mistay/s0http/media/IMG_1309.JPG

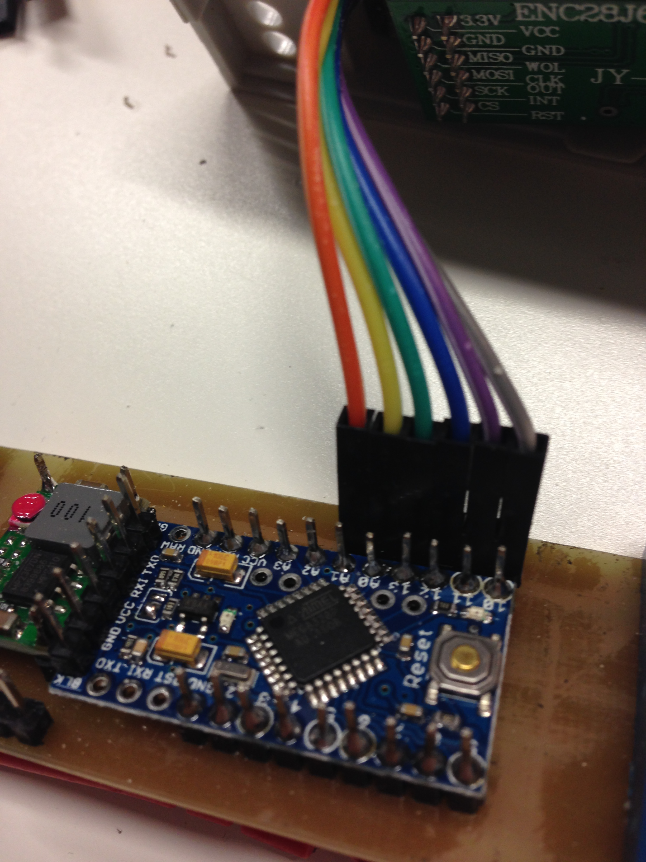
media/IMG_1309.JPG
