mistay/s0http/media/IMG_1310.JPG

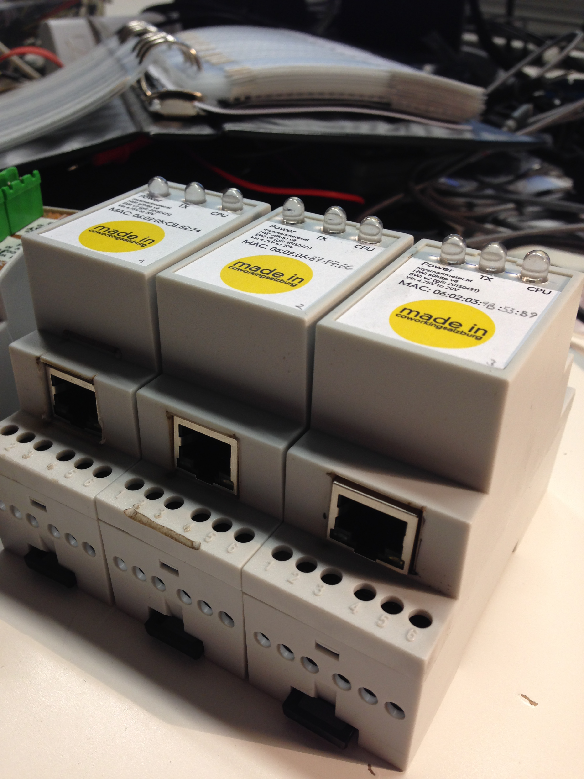
media/IMG_1310.JPG
