mistay/s0http/media/IMG_1311.JPG

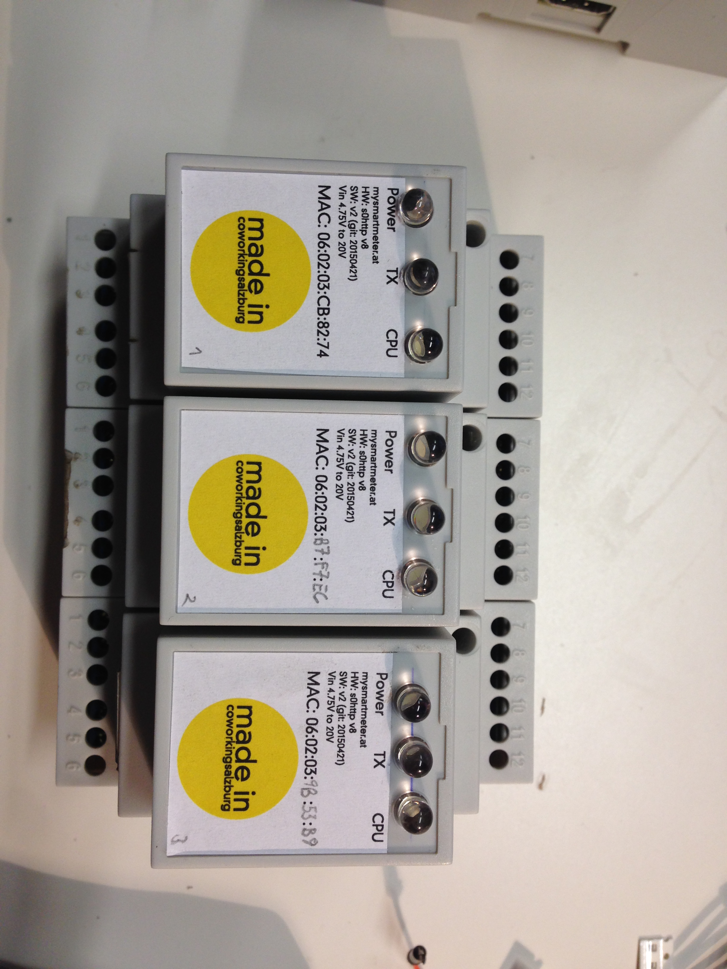
media/IMG_1311.JPG
