mistay/s0http/media/IMG_1312.JPG

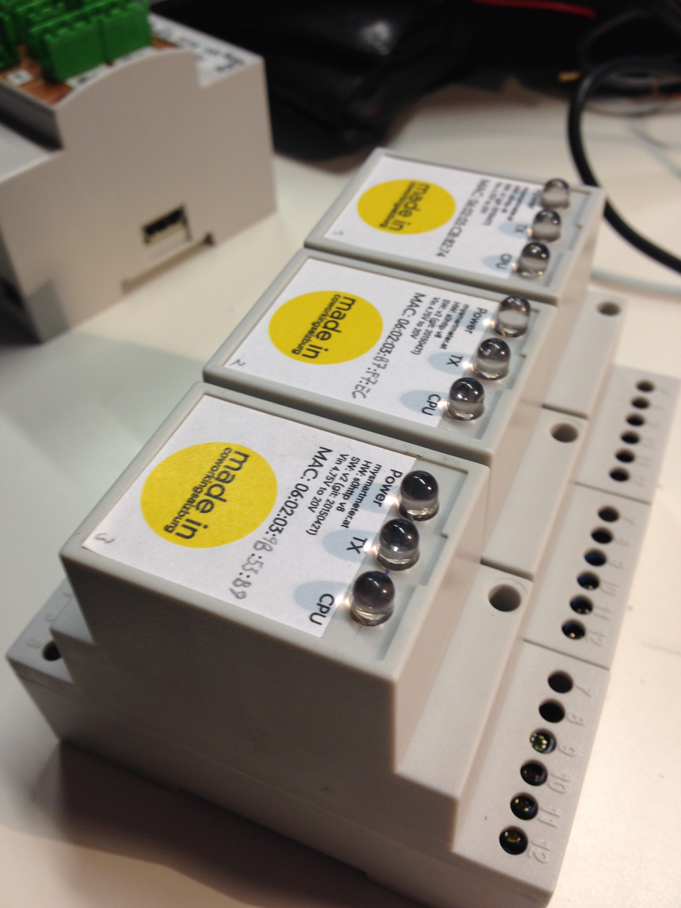
media/IMG_1312.JPG
