mistay/s0http/media/IMG_1313.JPG

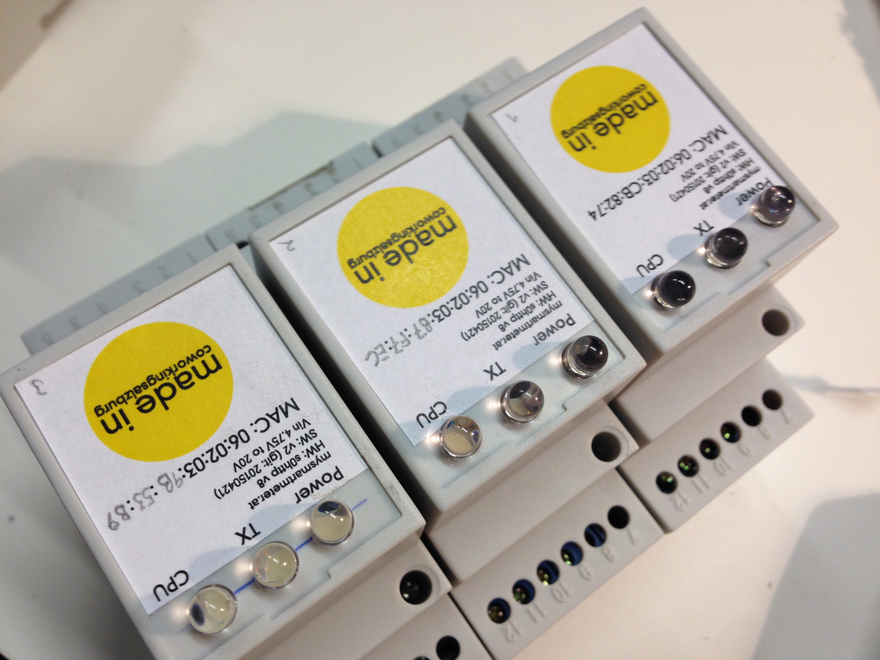
media/IMG_1313.JPG
