mistay/s0http/media/IMG_1314.JPG

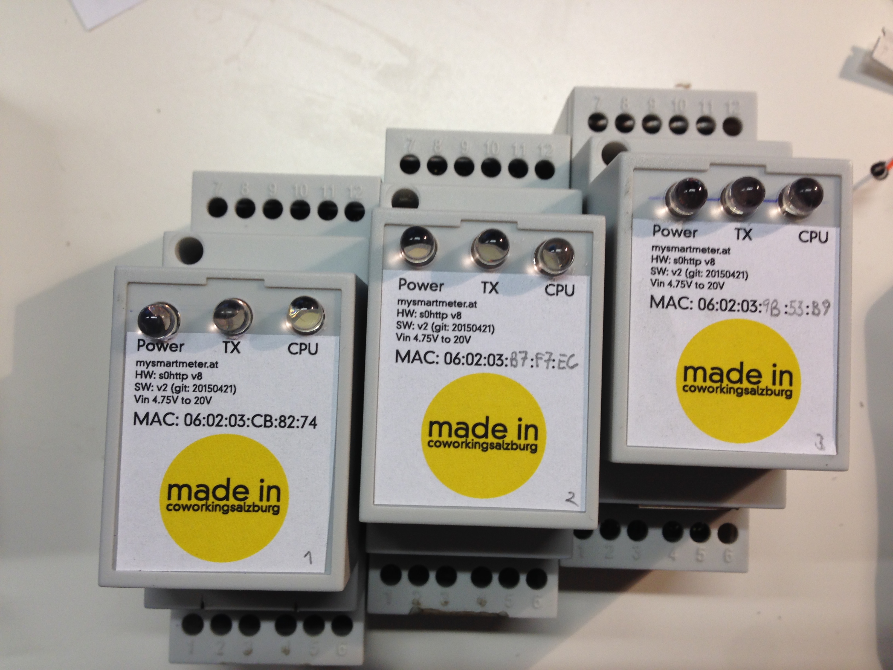
media/IMG_1314.JPG
