mistay/s0http/media/IMG_6536.JPG

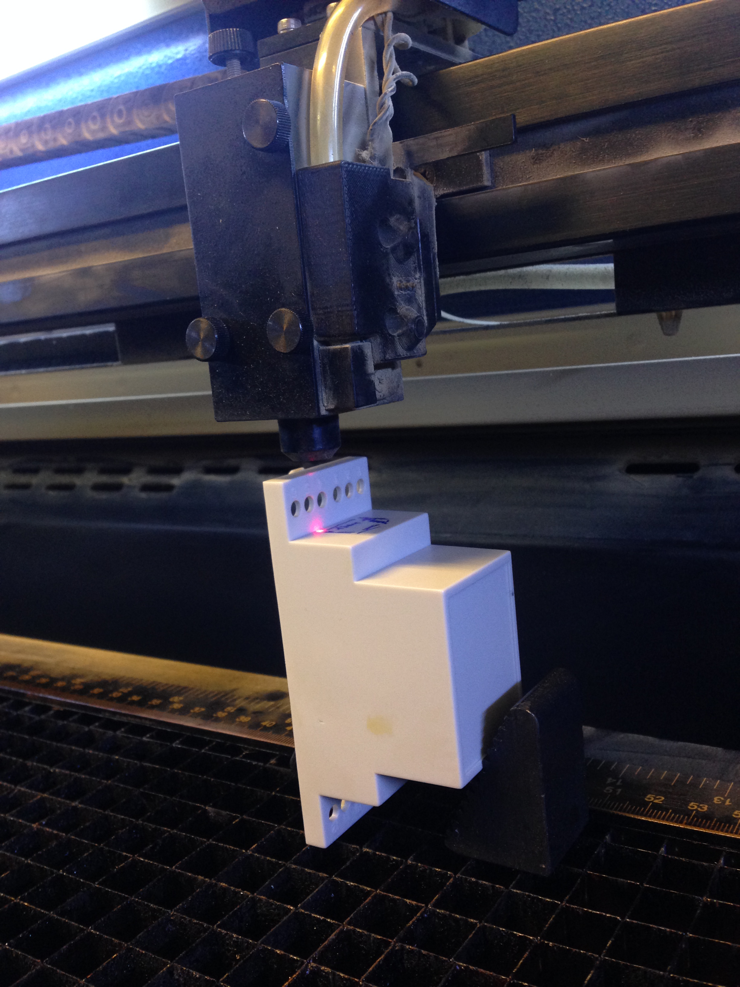
media/IMG_6536.JPG
