mistay/s0http/media/IMG_6537.JPG

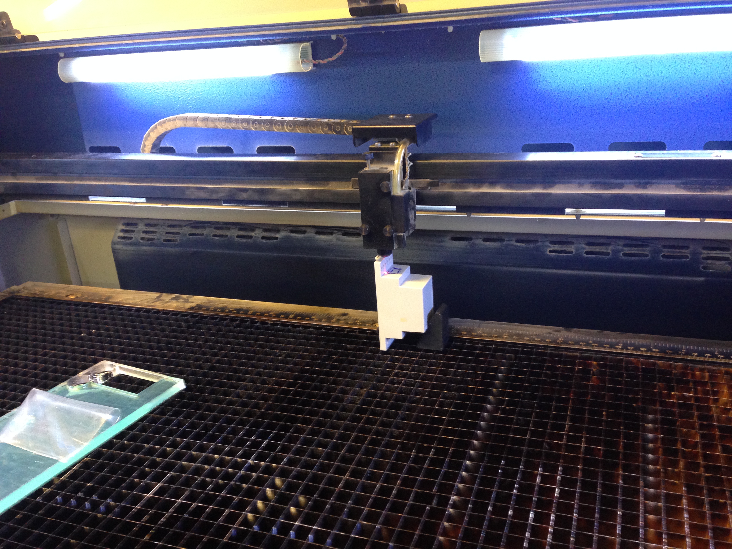
media/IMG_6537.JPG
