mistay/s0http/media/IMG_6538.JPG

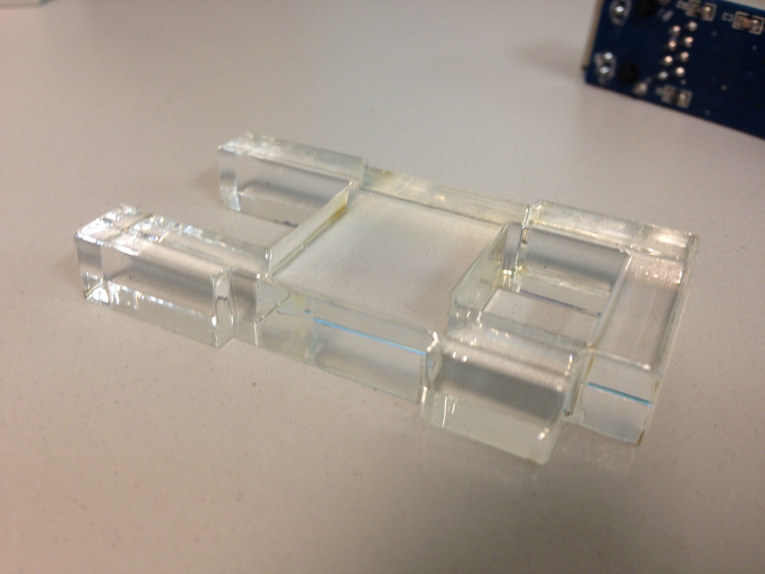
media/IMG_6538.JPG
