mistay/s0http/media/IMG_6539.JPG

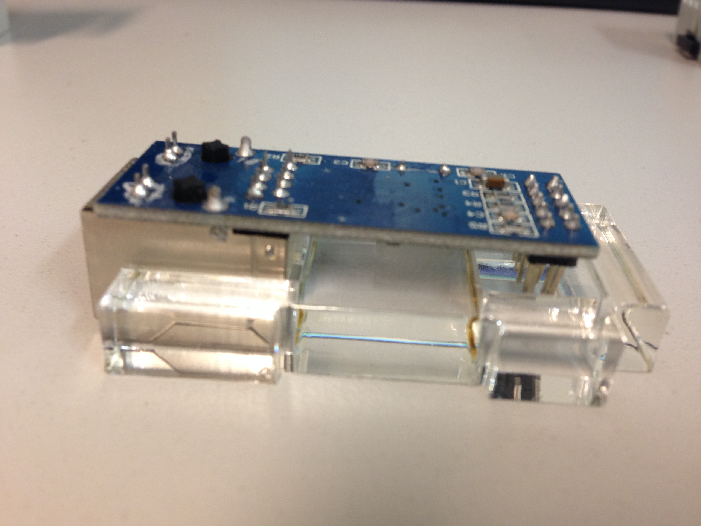
media/IMG_6539.JPG
