mistay/s0http/media/IMG_6540.JPG

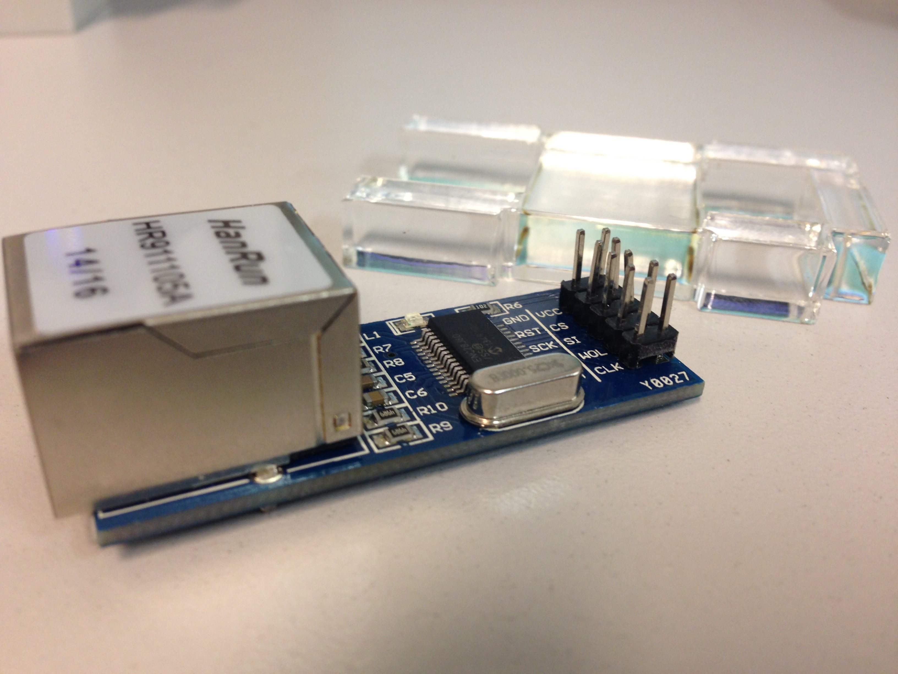
media/IMG_6540.JPG
