mistay/s0http/media/IMG_6542.JPG

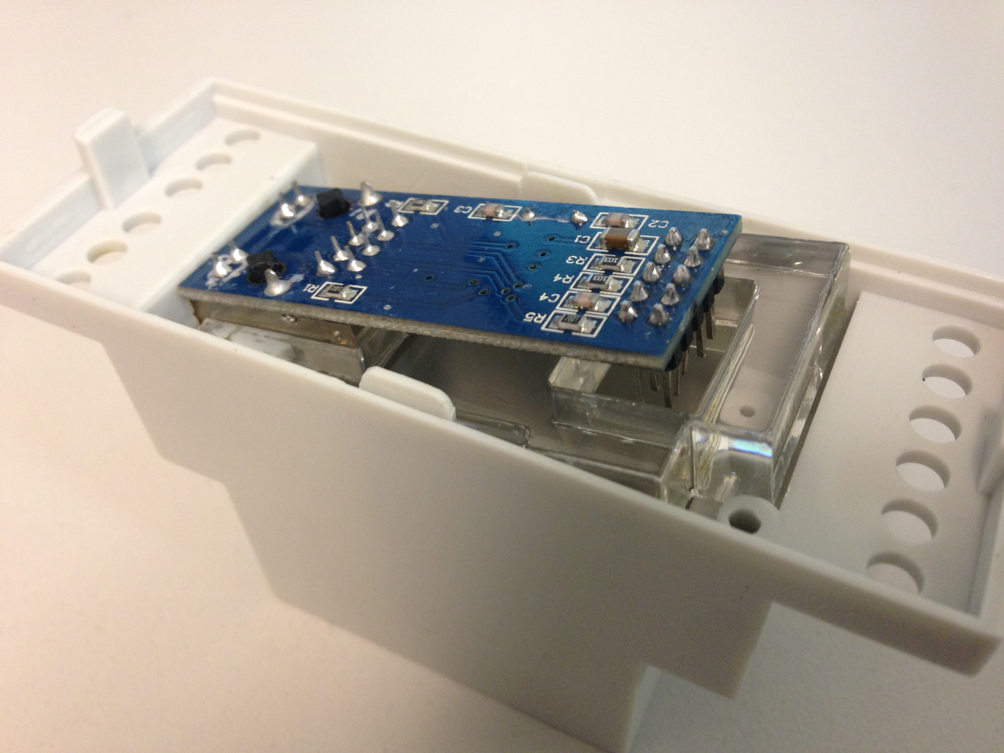
media/IMG_6542.JPG
