mistay/s0http/media/IMG_6543.JPG

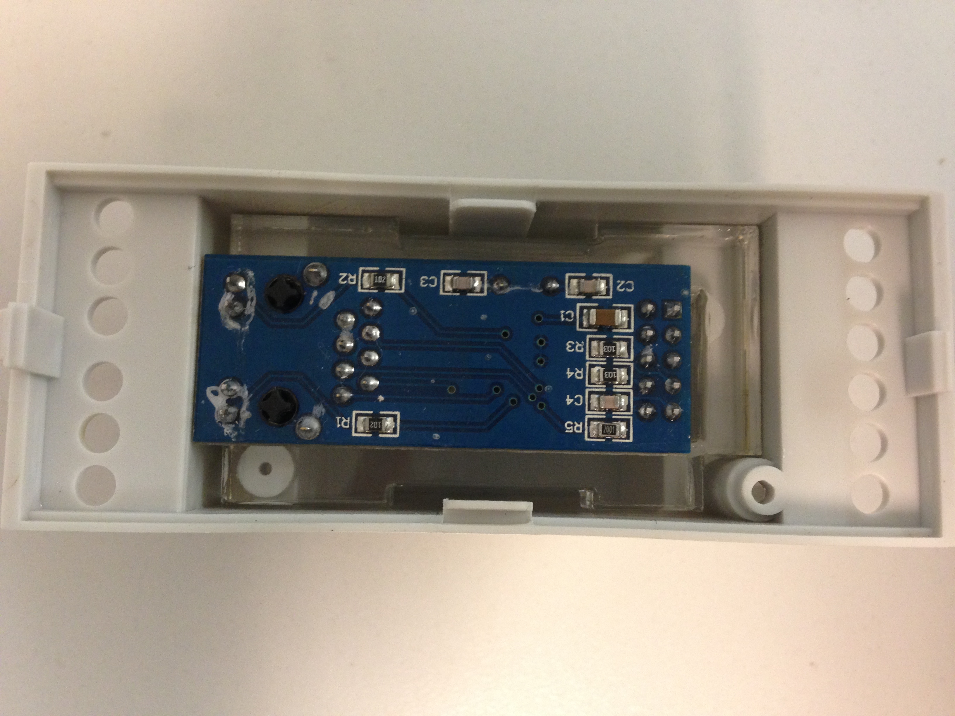
media/IMG_6543.JPG
