mistay/s0http/media/IMG_6544.JPG

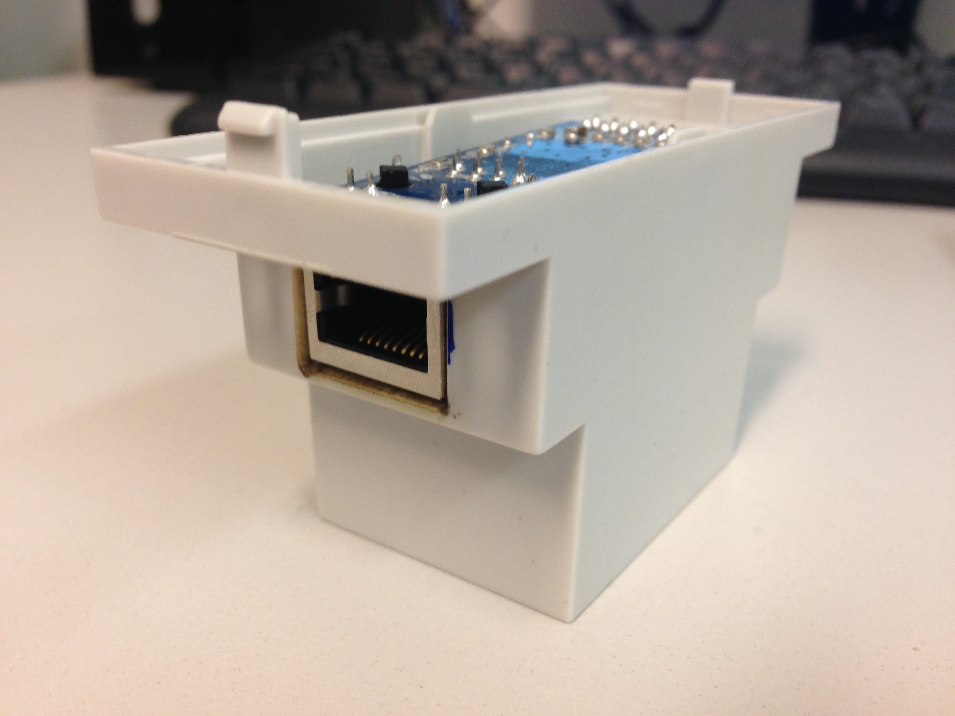
media/IMG_6544.JPG
