mistay/s0http/media/IMG_7528.JPG

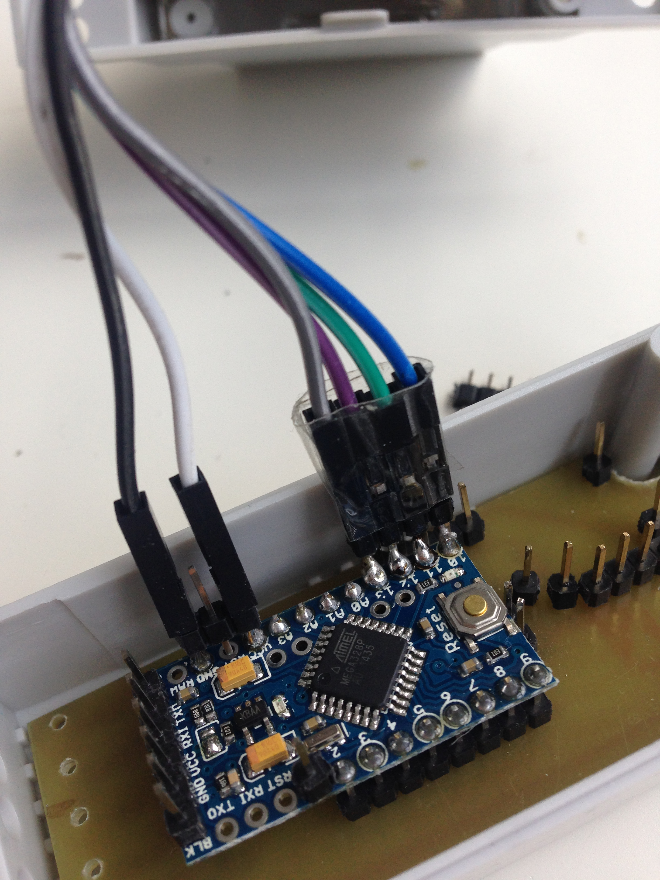
media/IMG_7528.JPG
