mistay/s0http/media/IMG_7529.JPG

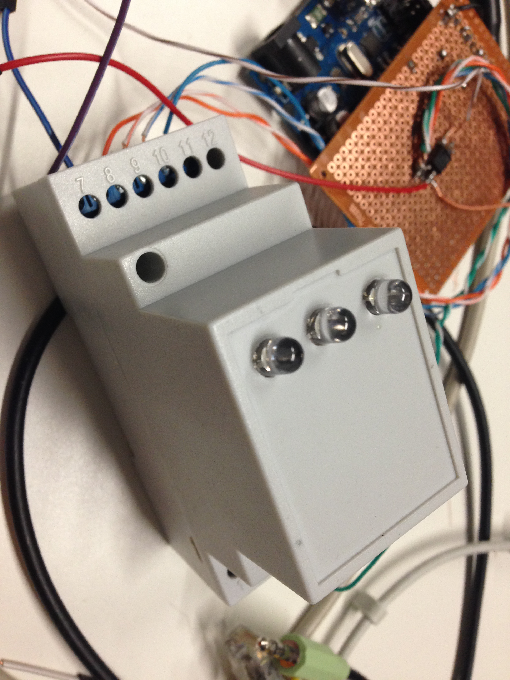
media/IMG_7529.JPG
