mistay/s0http/media/IMG_7530.JPG

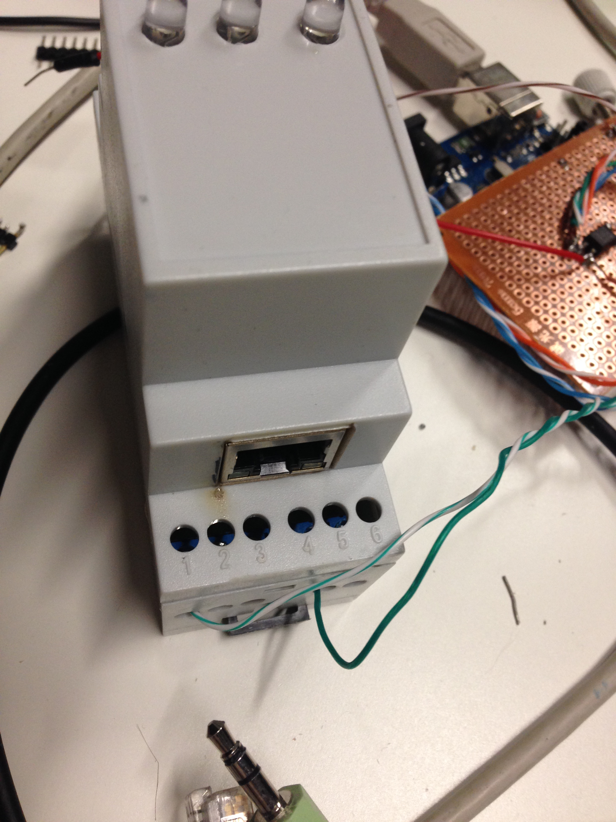
media/IMG_7530.JPG
