mistay/s0http/media/IMG_7531.JPG

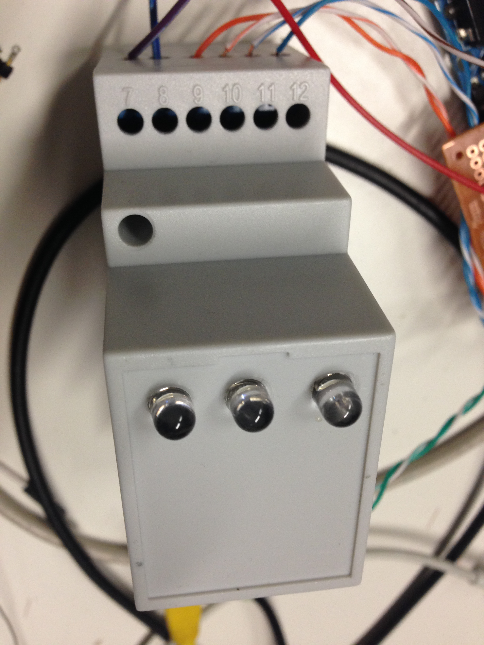
media/IMG_7531.JPG
