mistay/s0http/media/IMG_7536.JPG

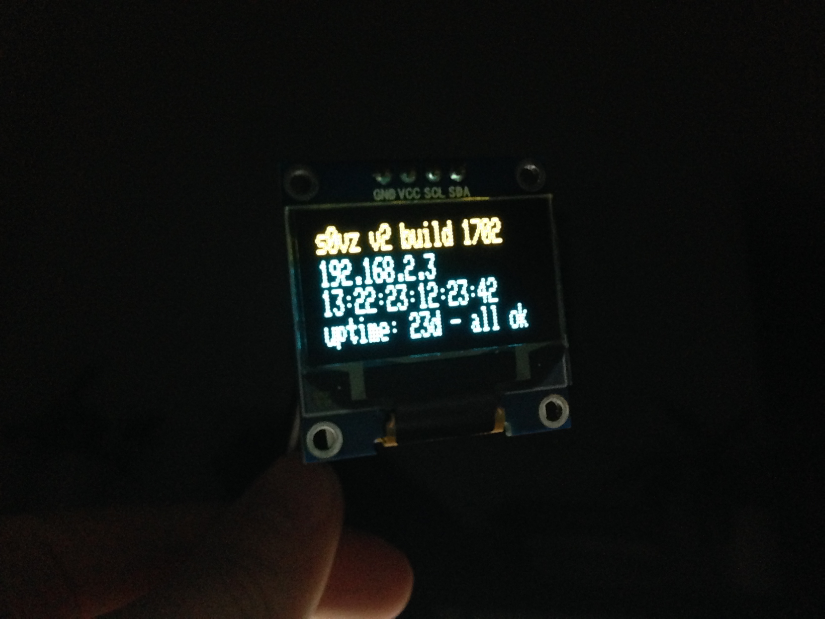
media/IMG_7536.JPG
