mistay/s0http/media/IMG_7617.JPG

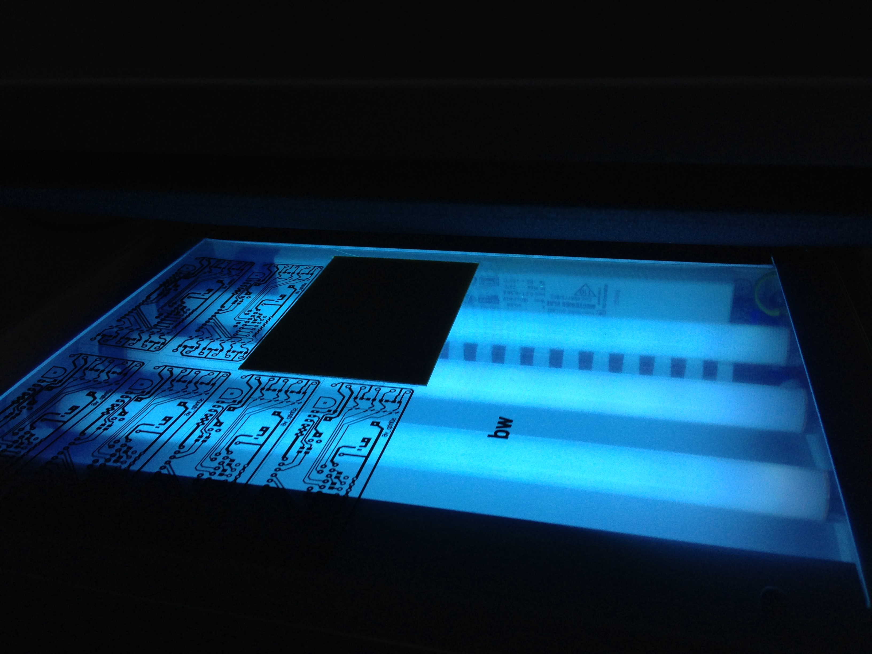
media/IMG_7617.JPG
