mistay/s0http/media/IMG_7618.JPG

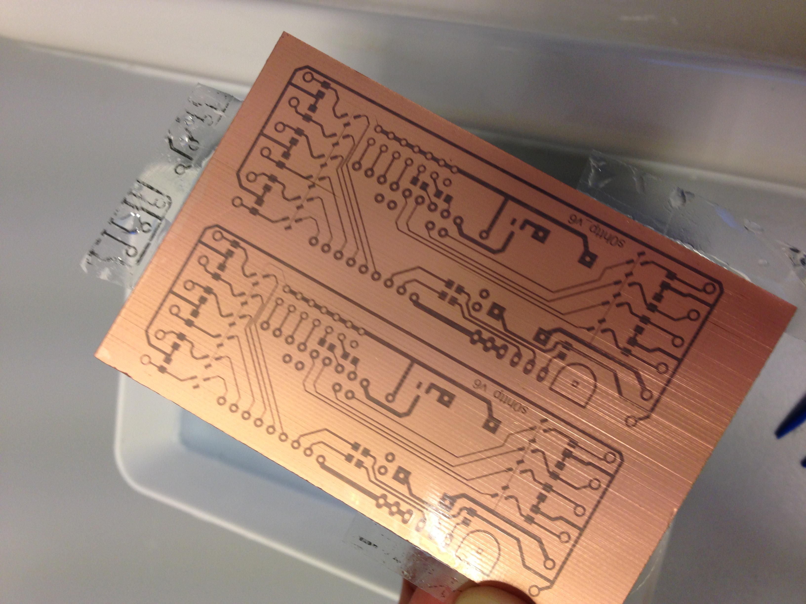
media/IMG_7618.JPG
