mistay/s0http/media/IMG_7619.JPG

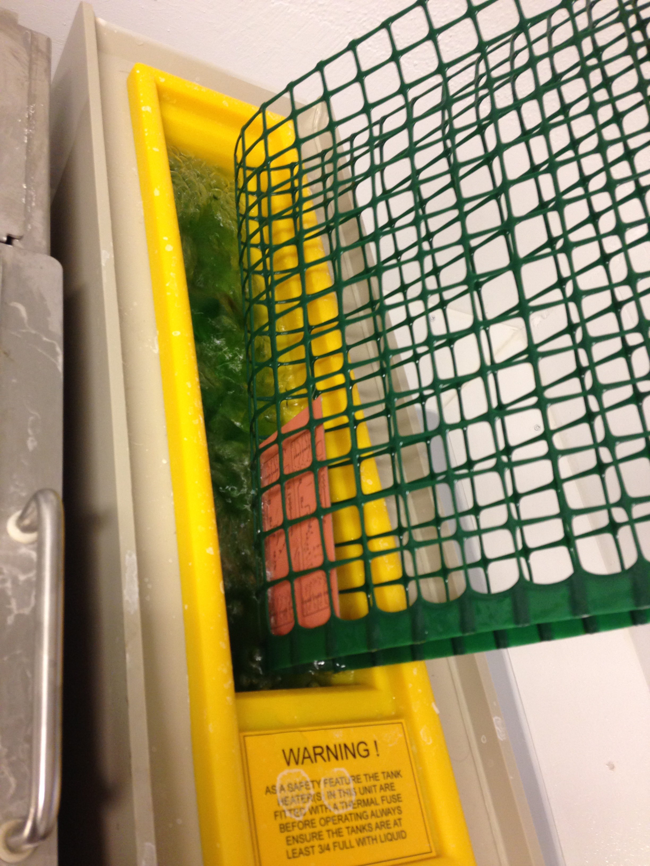
media/IMG_7619.JPG
