mistay/s0http/media/IMG_7620.JPG

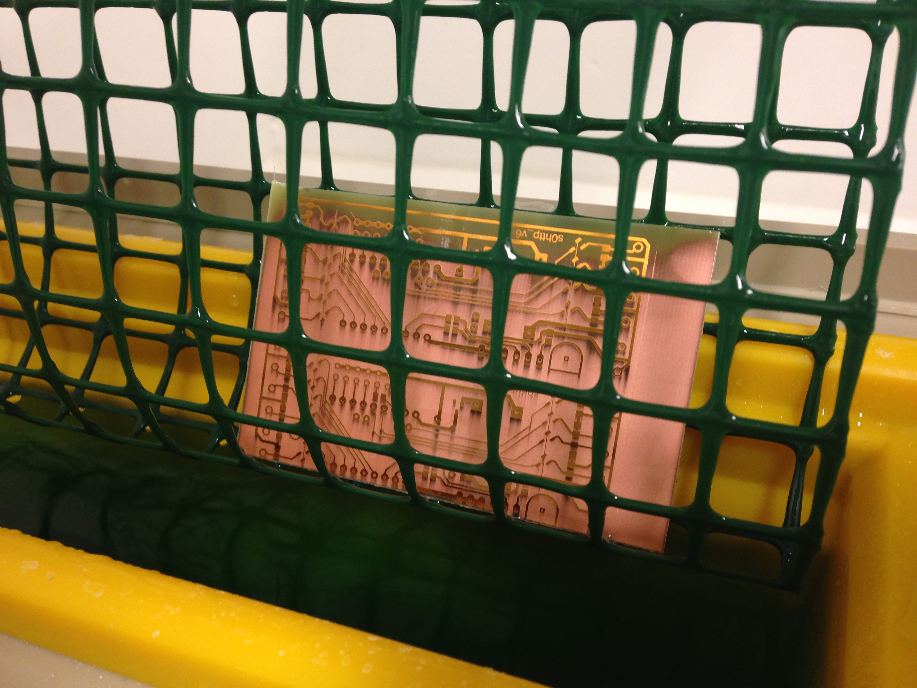
media/IMG_7620.JPG
