mistay/s0http/media/IMG_7635.JPG

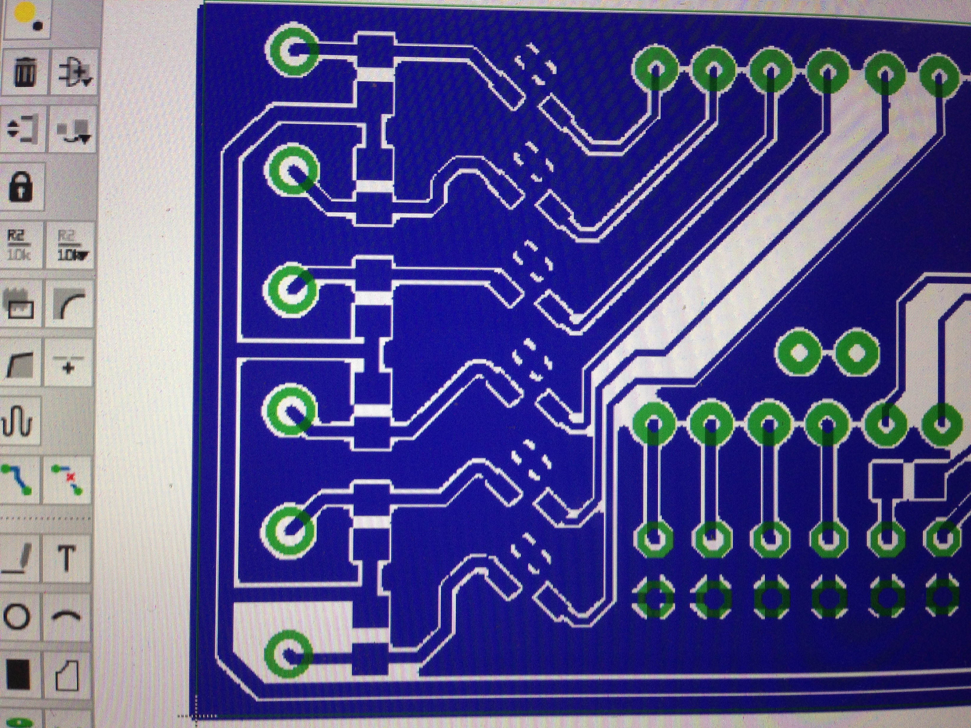
media/IMG_7635.JPG
