mistay/s0http/media/IMG_7978.JPG

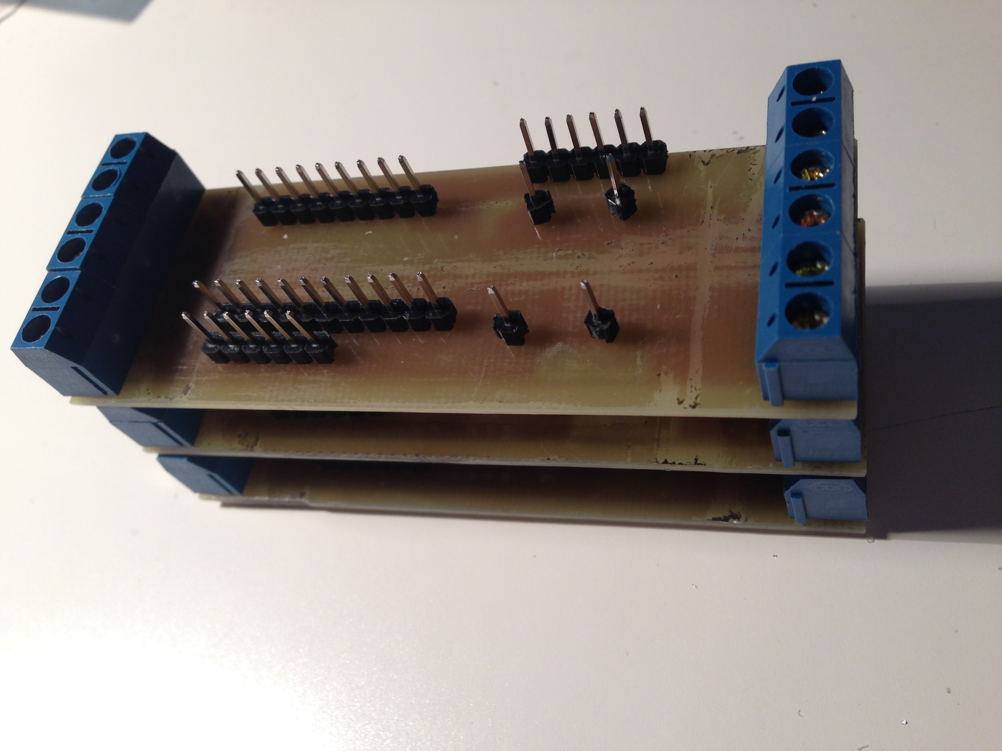
media/IMG_7978.JPG
