mistay/s0http/media/IMG_7979.JPG

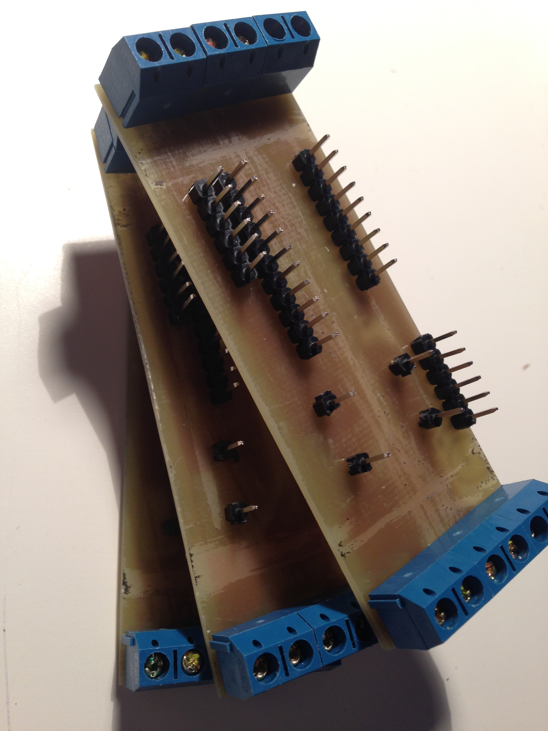
media/IMG_7979.JPG
