mistay/s0http/media/IMG_7980.JPG

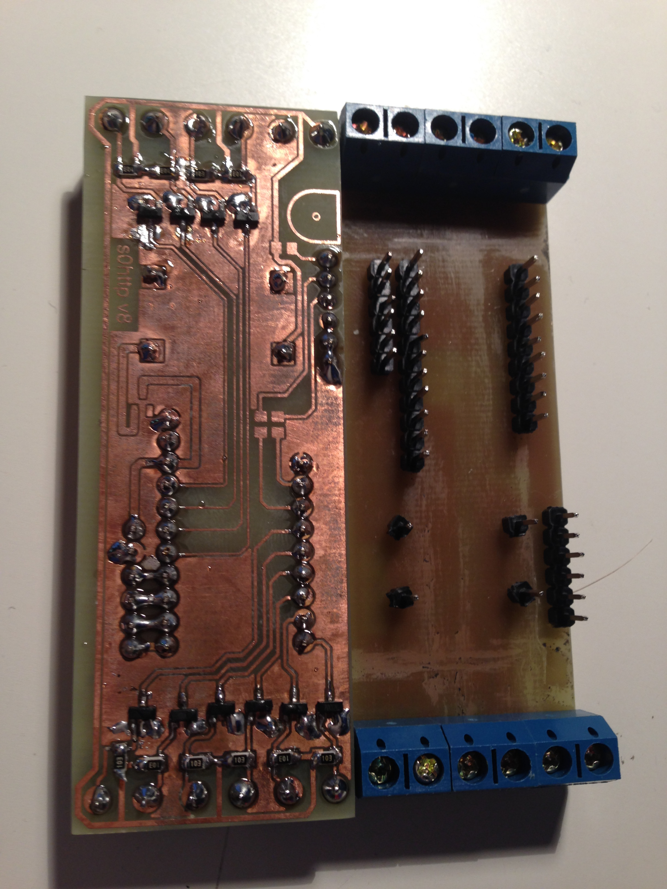
media/IMG_7980.JPG
