mistay/s0http/media/vz.png

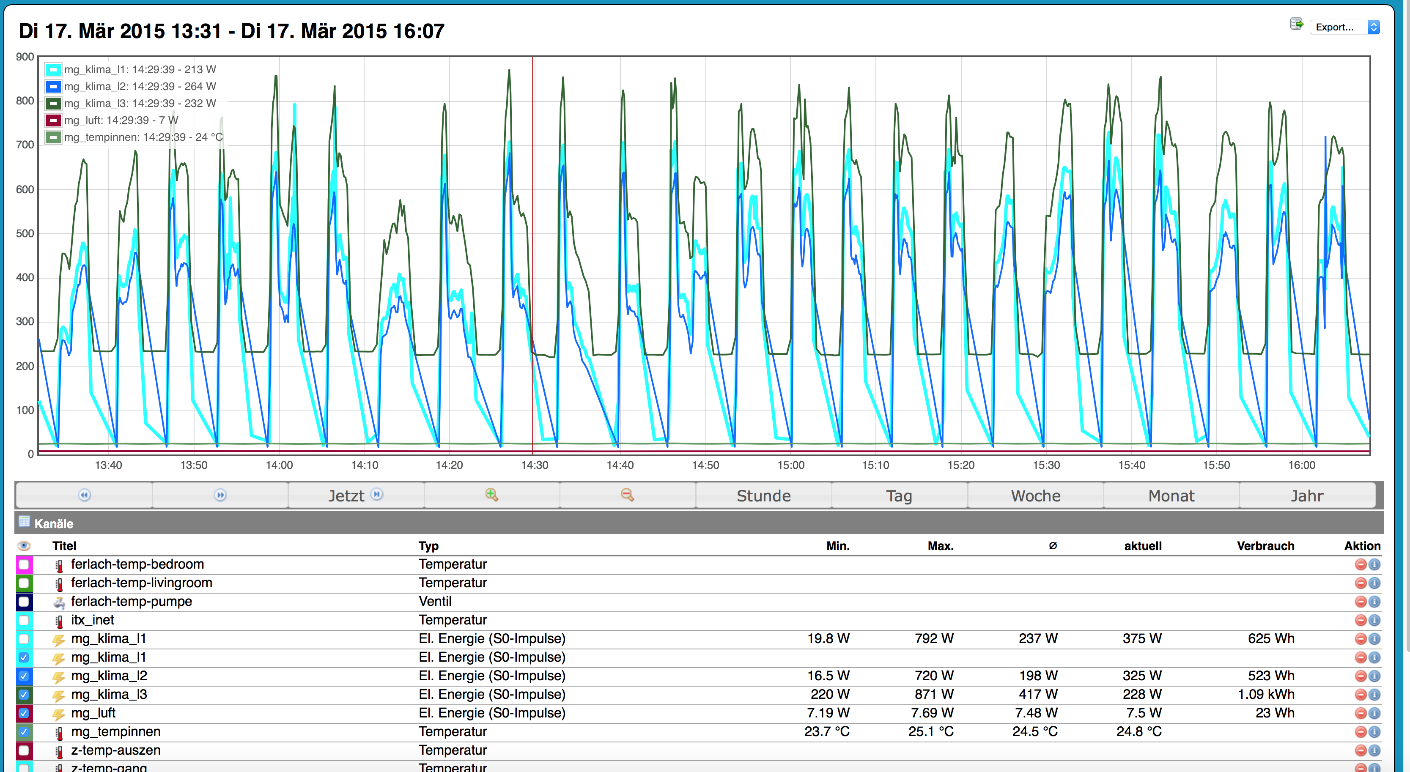
media/vz.png
